fra589/WeThermic/images/freecad00.png

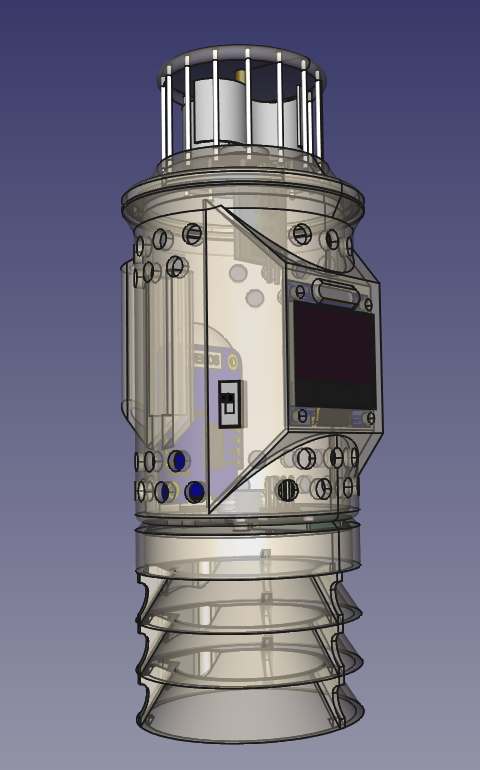
images/freecad00.png
