fra589/WeThermic/images/freecad01.png

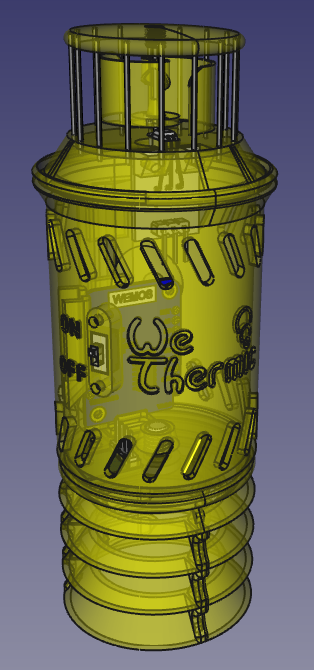
images/freecad01.png
