fra589/WeThermic/images/IMG_20240806_122609.jpg

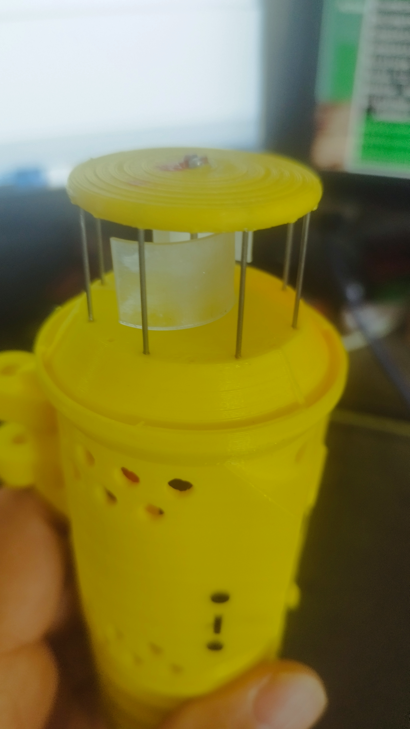
images/IMG_20240806_122609.jpg
