fra589/WeThermic/images/IMG_20240806_165015.jpg

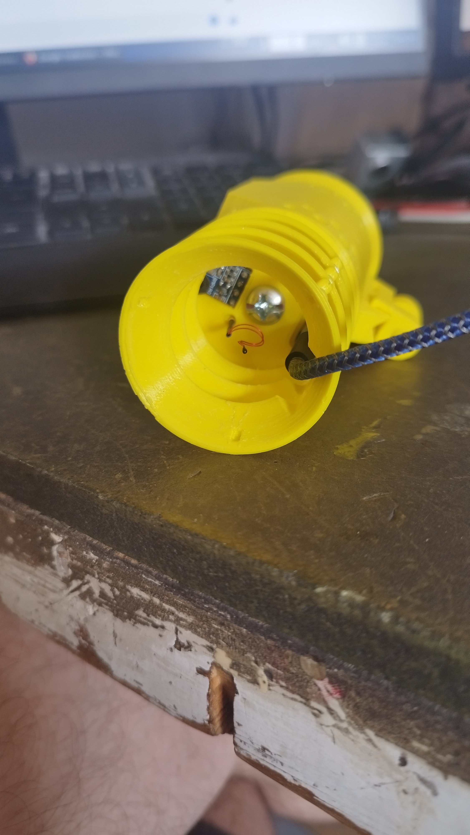
images/IMG_20240806_165015.jpg
