fra589/WeThermic/images/IMG_20240806_165026.jpg

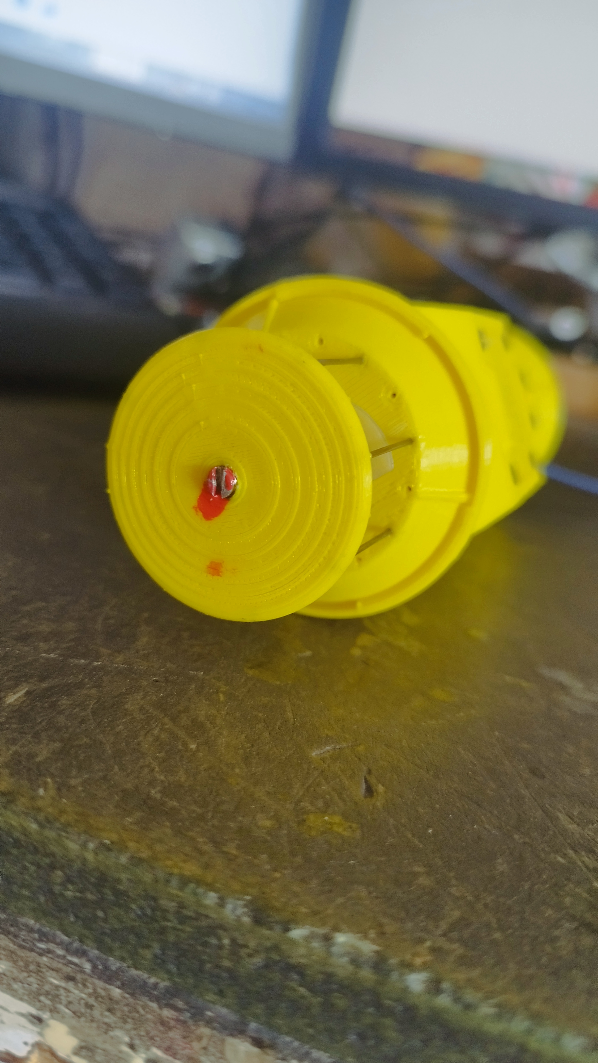
images/IMG_20240806_165026.jpg
