fra589/WeThermic/images/IMG_20240806_165034.jpg

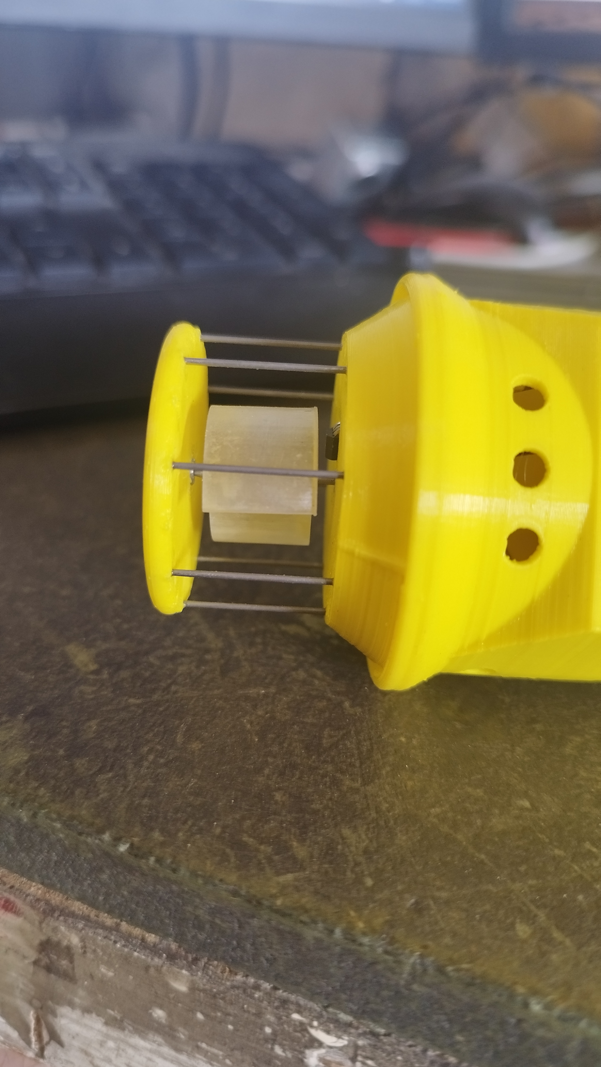
images/IMG_20240806_165034.jpg
