fra589/WeThermic/images/IMG_20240806_165058.jpg

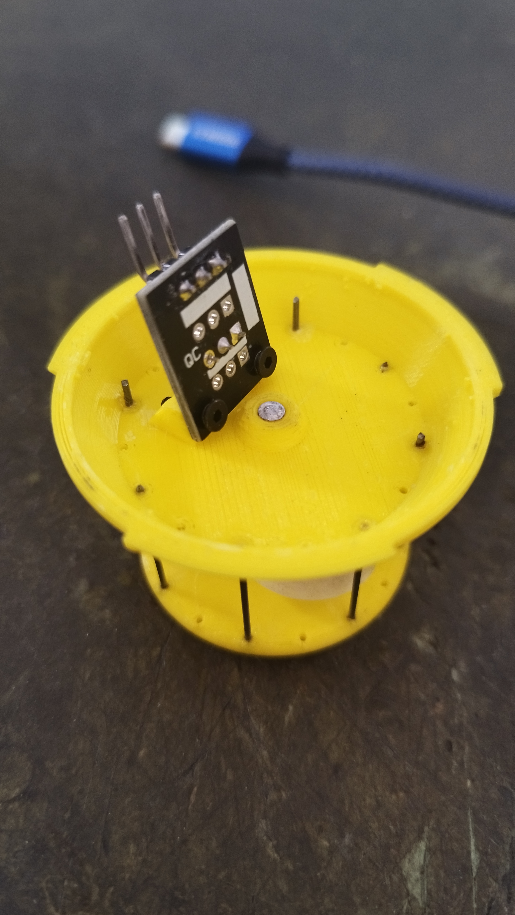
images/IMG_20240806_165058.jpg
