fra589/WeThermic/images/IMG_20240806_165123.jpg

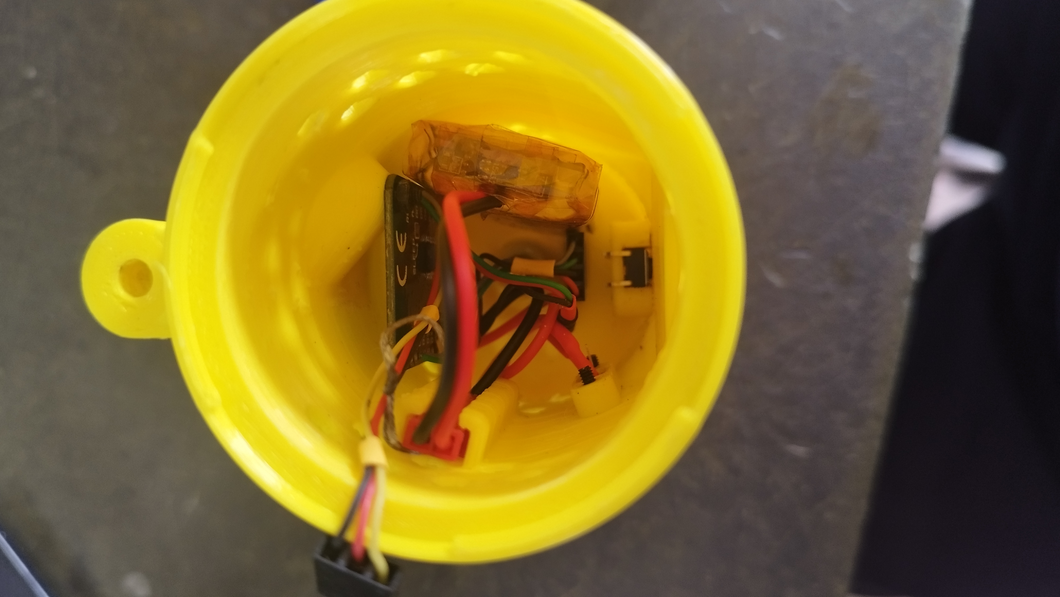
images/IMG_20240806_165123.jpg
