fra589/WeThermic/images/IMG_20240810_173007.jpg

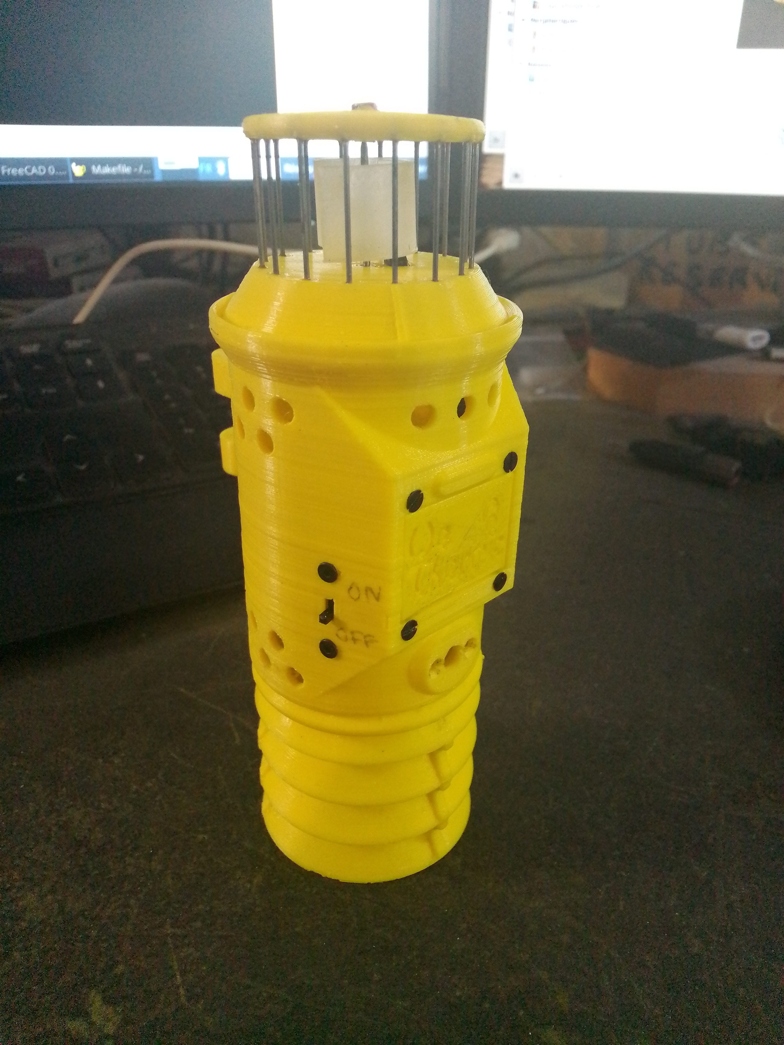
images/IMG_20240810_173007.jpg
