fra589/WeThermic/images/IMG_20240811_102927.jpg

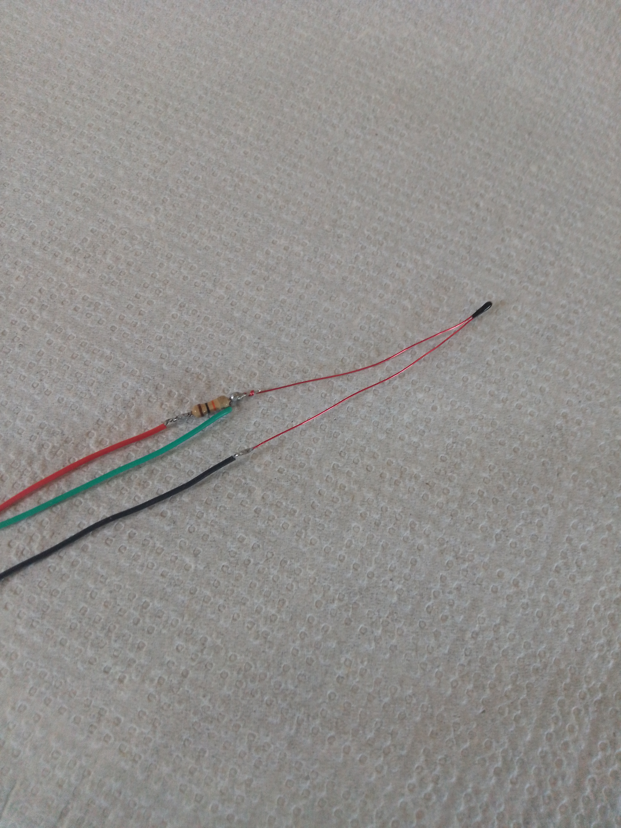
images/IMG_20240811_102927.jpg
