fra589/WeThermic/images/IMG_20240811_103149.jpg

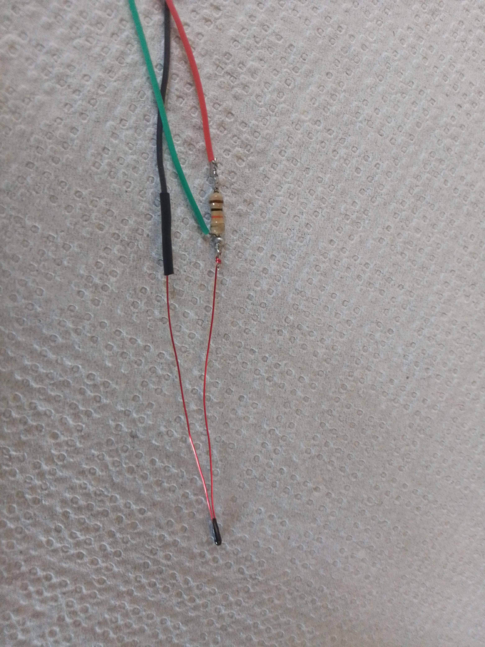
images/IMG_20240811_103149.jpg
