fra589/WeThermic/images/IMG_20240811_103520.jpg

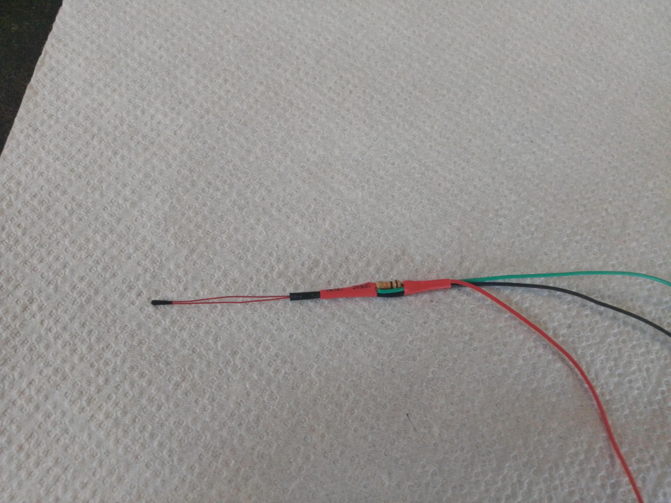
images/IMG_20240811_103520.jpg
