fra589/WeThermic/images/IMG_20240811_115443.jpg

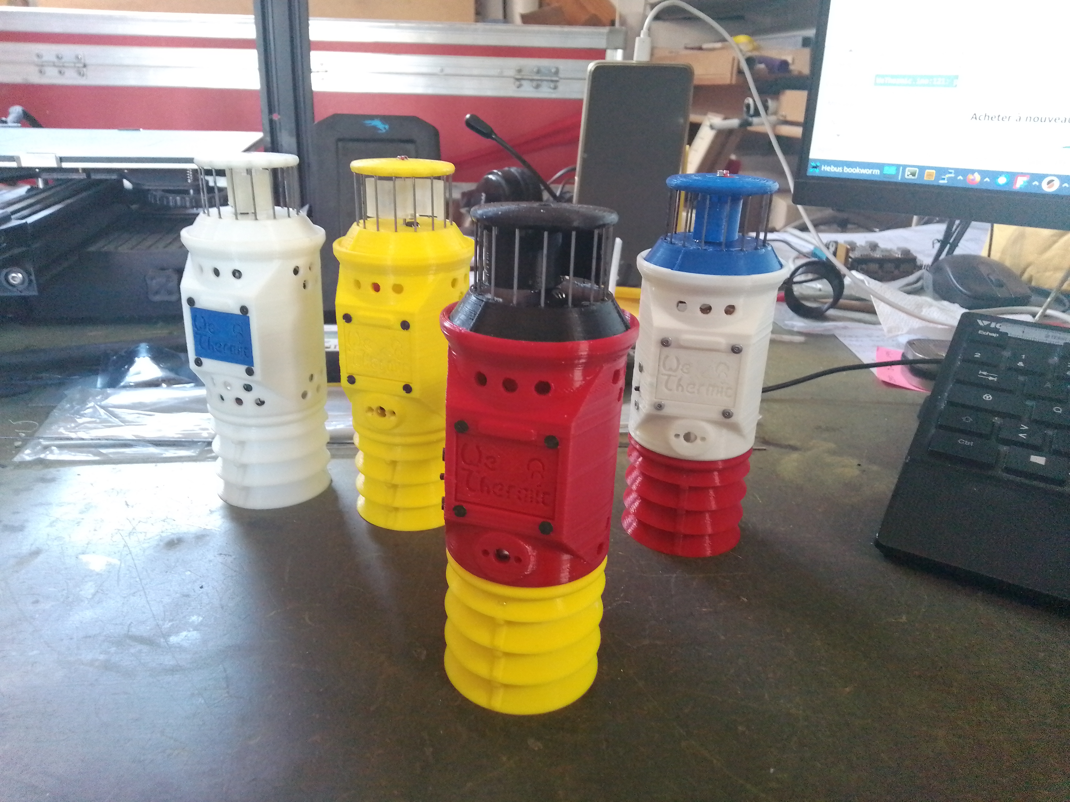
images/IMG_20240811_115443.jpg
