fra589/WeThermic/images/IMG_20250127_192134.jpg

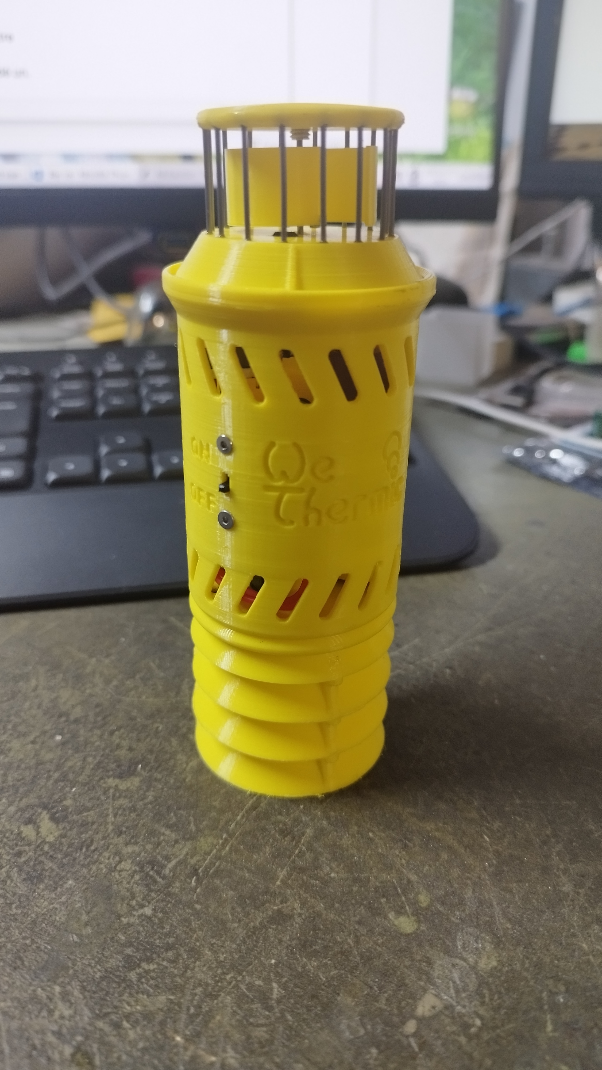
images/IMG_20250127_192134.jpg
