fra589/WeThermic/images/Screenshot_20240810-114502.png

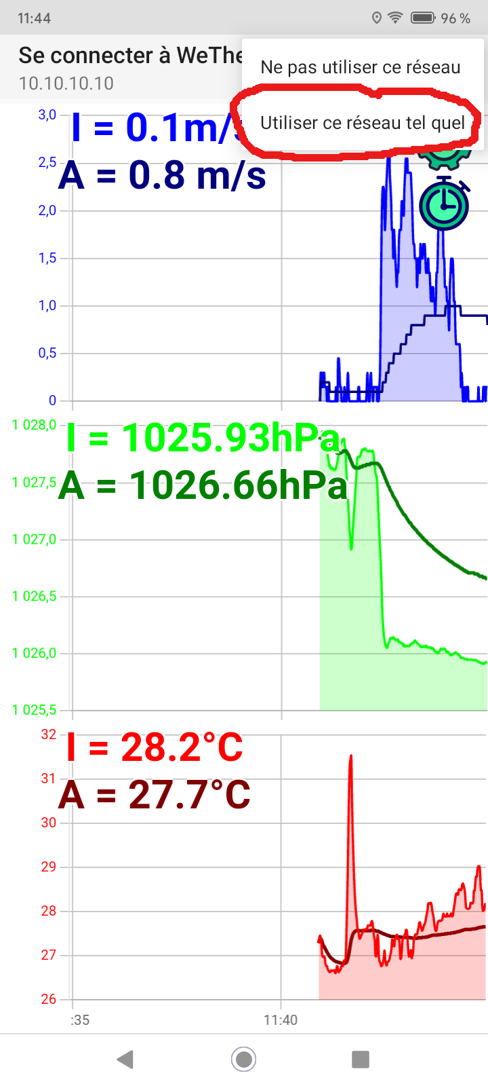
images/Screenshot_20240810-114502.png
