fra589/WeThermic/images/Screenshot_20240810-114620.png

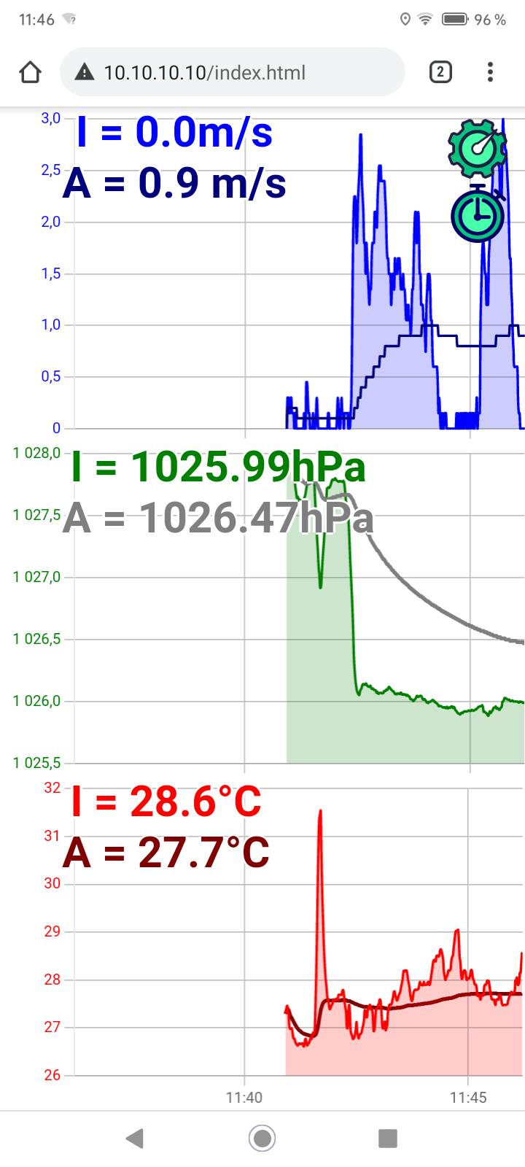
images/Screenshot_20240810-114620.png
