fra589/WeThermic/images/Screenshot_20240810-114928.png

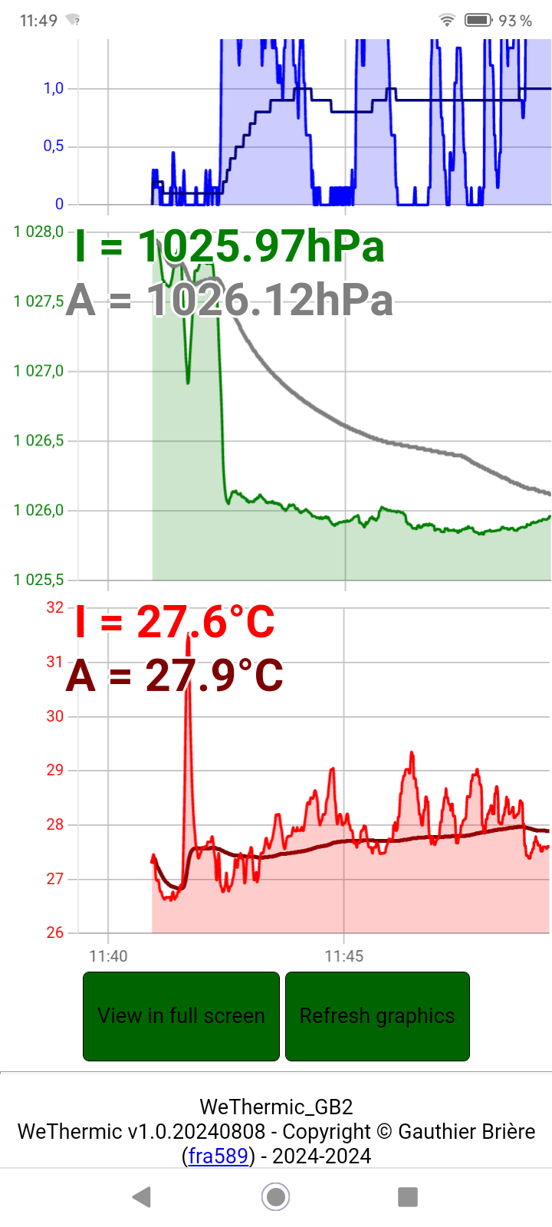
images/Screenshot_20240810-114928.png
