fra589/WeThermic/images/Screenshot_20240810-121120.png

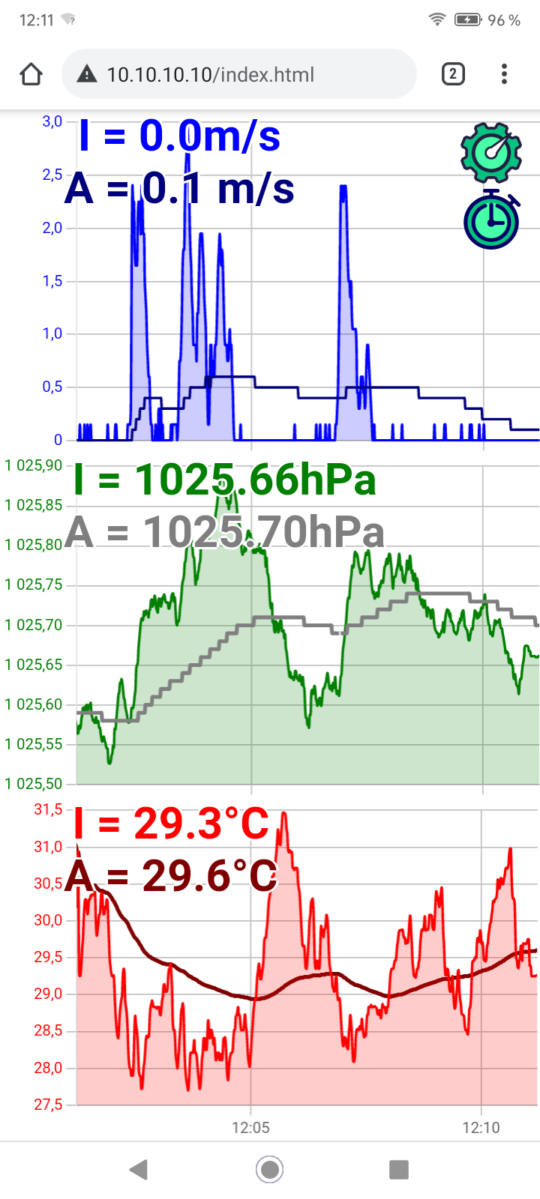
images/Screenshot_20240810-121120.png
