fra589/WeThermic/images/Screenshot_20240810-121140.png

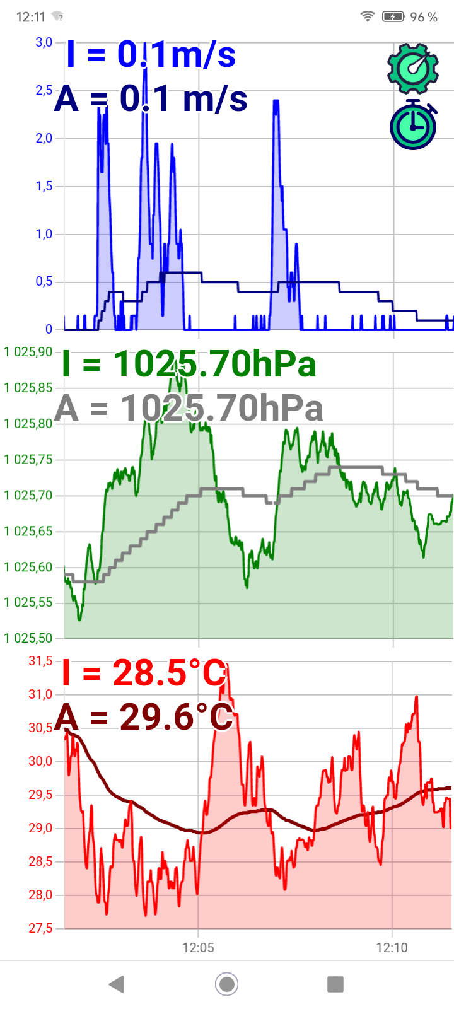
images/Screenshot_20240810-121140.png
