fra589/WeThermic/images/Screenshot_20240810-172216.png

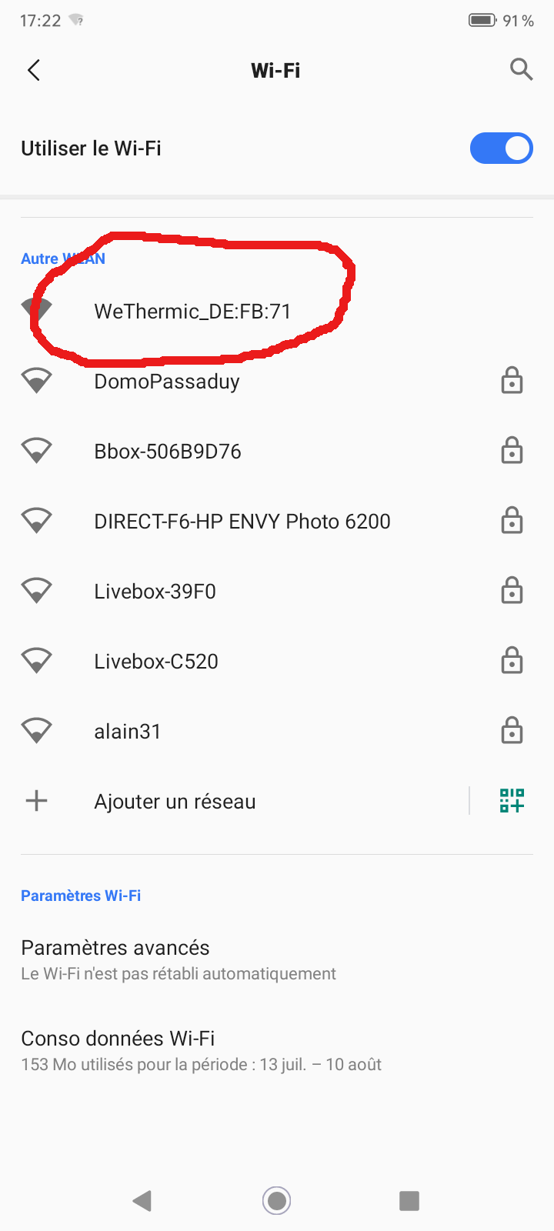
images/Screenshot_20240810-172216.png
