fra589/WeThermic/images/Screenshot_20240810-172354.png

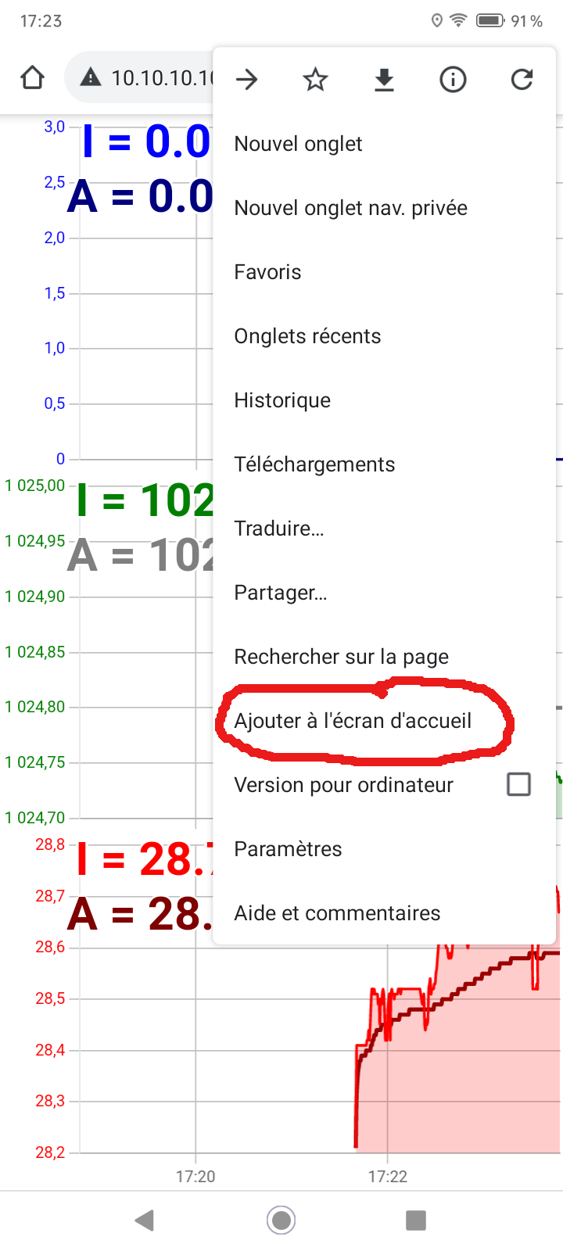
images/Screenshot_20240810-172354.png
