fra589/WeThermic/images/Screenshot_20240810-173539.png

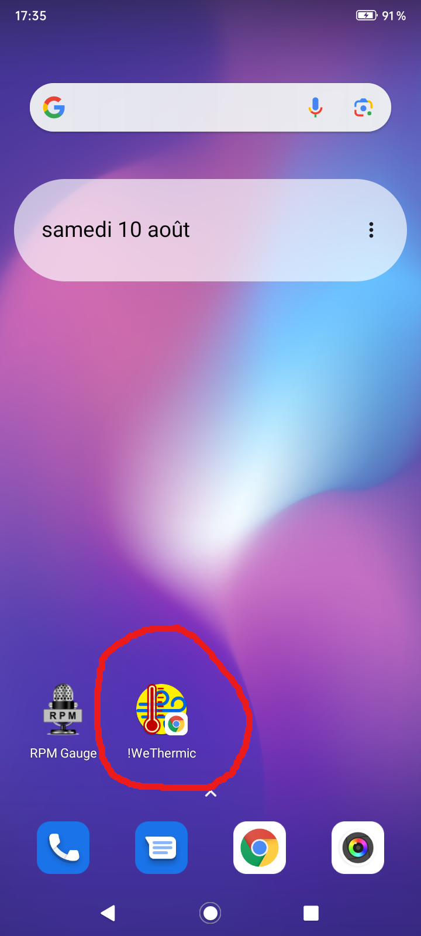
images/Screenshot_20240810-173539.png
