fra589/WeThermic/images/Screenshot_20240811-184933.png

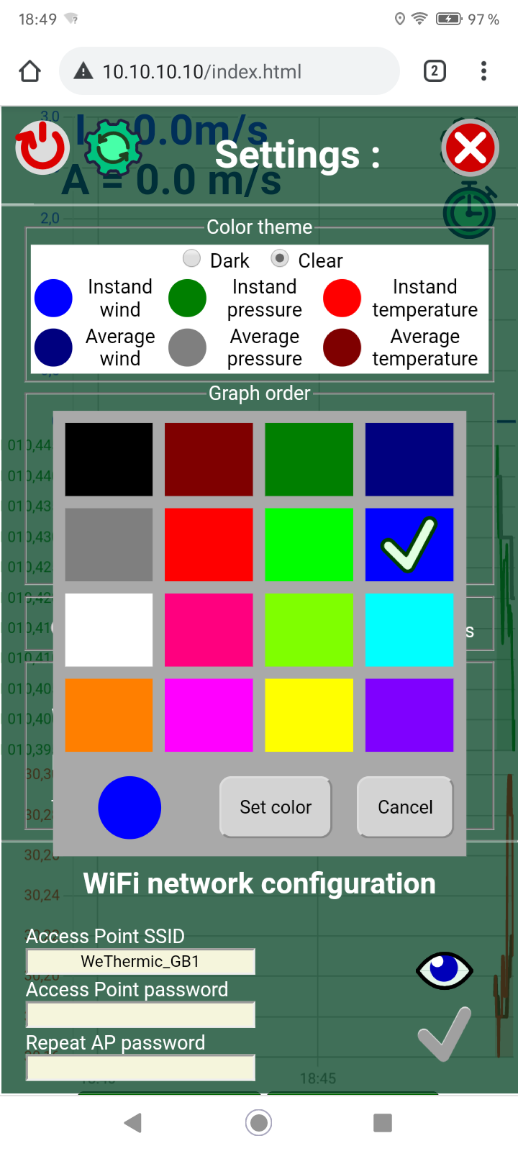
images/Screenshot_20240811-184933.png
