fra589/WeThermic/images/Screenshot_20240826-163647.png

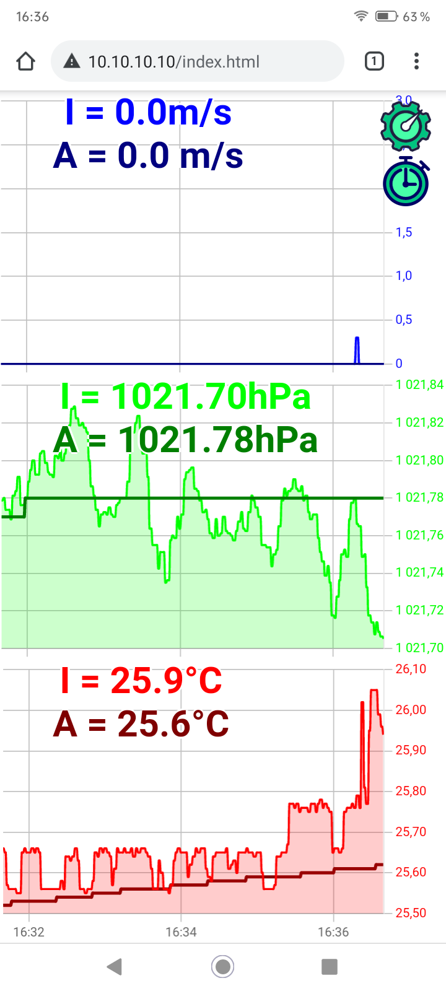
images/Screenshot_20240826-163647.png
