fra589/WeThermic/images/Screenshot_20240826-163702.png

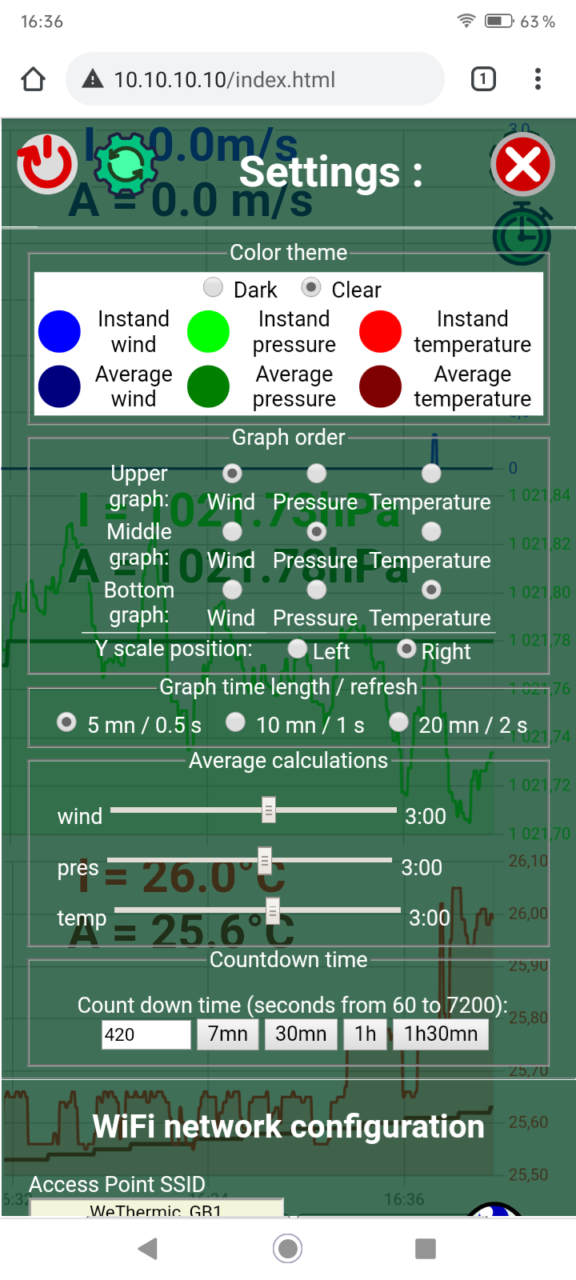
images/Screenshot_20240826-163702.png
