fra589/WeThermic/images/StationMarc.jpeg

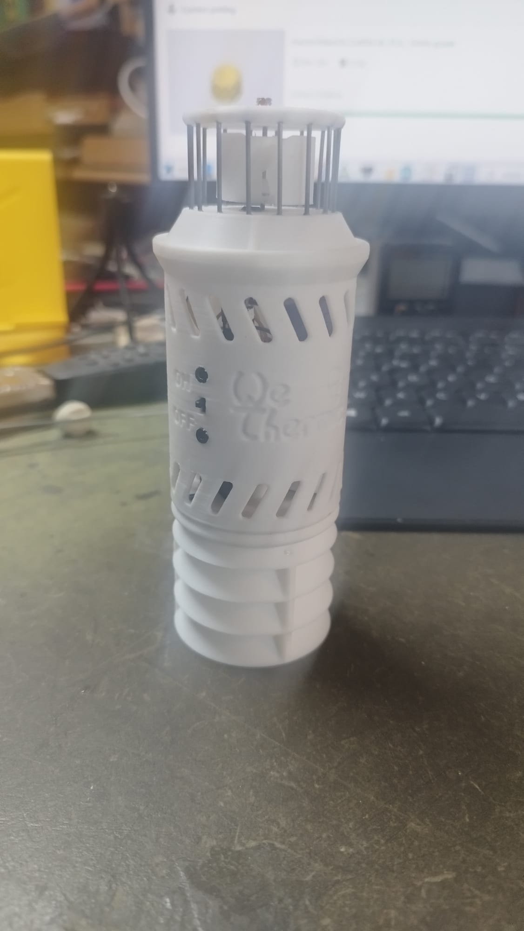
images/StationMarc.jpeg
