fra589/WeThermic/WeThermic/WeThermicLogo.h

/****************************************************************************/
/*                                                                          */
/* Copyright (C) 2024-2025 Gauthier Brière (gauthier.briere "at" gmail.com) */
/*                                                                          */
/* This file: WeThermicLogo.h is part of WeThermic                          */
/*                                                                          */
/* WeThermic is free software: you can redistribute it and/or modify it     */
/* under the terms of the GNU General Public License as published by        */
/* the Free Software Foundation, either version 3 of the License, or        */
/* (at your option) any later version.                                      */
/*                                                                          */
/* WeThermic is distributed in the hope that it will be useful, but         */
/* WITHOUT ANY WARRANTY; without even the implied warranty of               */
/* MERCHANTABILITY or FITNESS FOR A PARTICULAR PURPOSE.  See the            */
/* GNU General Public License for more details.                             */
/*                                                                          */
/* You should have received a copy of the GNU General Public License        */
/* along with this program.  If not, see <http://www.gnu.org/licenses/>.    */
/*                                                                          */
/****************************************************************************/
// Converti depuis PNG palette 2 couleurs par :
// https://notisrac.github.io/FileToCArray/

#define WETHERMICLOGO_HEIGHT 64
#define WETHERMICLOGO_WIDTH 128

// array size is 1024
static const uint8_t WeThermicLogo[] PROGMEM  = {
  B00000001, B10000000, B00000011, B00000000, B00000000, B00000000, B00000000, B00000000, B00000000, B00000000, B00000000, B00000000, B00000000, B00000000, B00000000, B00000000, 
  B00000011, B11000000, B00000111, B10000000, B00000000, B00000000, B00000000, B00000000, B00000000, B00000000, B00000000, B00000000, B00000000, B00000000, B00000000, B00000000, 
  B00000111, B11000000, B00000111, B11000000, B00000000, B00000000, B00000000, B00000000, B00000000, B00000000, B00000000, B00000000, B00000000, B00000000, B00000000, B00000000, 
  B00001111, B11000000, B00000111, B11100000, B00000000, B00000000, B00000000, B00000000, B00000000, B00000000, B00000000, B00000000, B00000000, B00000000, B00000000, B00000000, 
  B00011111, B11000000, B00000111, B11110000, B00000000, B00000000, B00000000, B00000000, B00000000, B00000000, B00000000, B00000000, B00001111, B11111100, B00000000, B00000000, 
  B00011111, B10000000, B00000011, B11110000, B00000000, B00000000, B00000000, B00000000, B00000000, B00000000, B00000000, B00000000, B00111111, B11111111, B00000000, B00000000, 
  B00111111, B00000000, B00000001, B11111000, B00000000, B00000000, B00000000, B00000000, B00000000, B00000000, B00000000, B00000000, B01111111, B11111111, B10000000, B00000000, 
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
  B00000000, B00001111, B10000000, B00000000, B11111000, B00000000, B00000000, B00000000, B00000000, B00000000, B00000000, B00000000, B00000000, B00111111, B10000000, B00000000, 
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
};
